speedypotato/Pocket-SDVX/IMAGES/screenshots/100OhmResistor.png

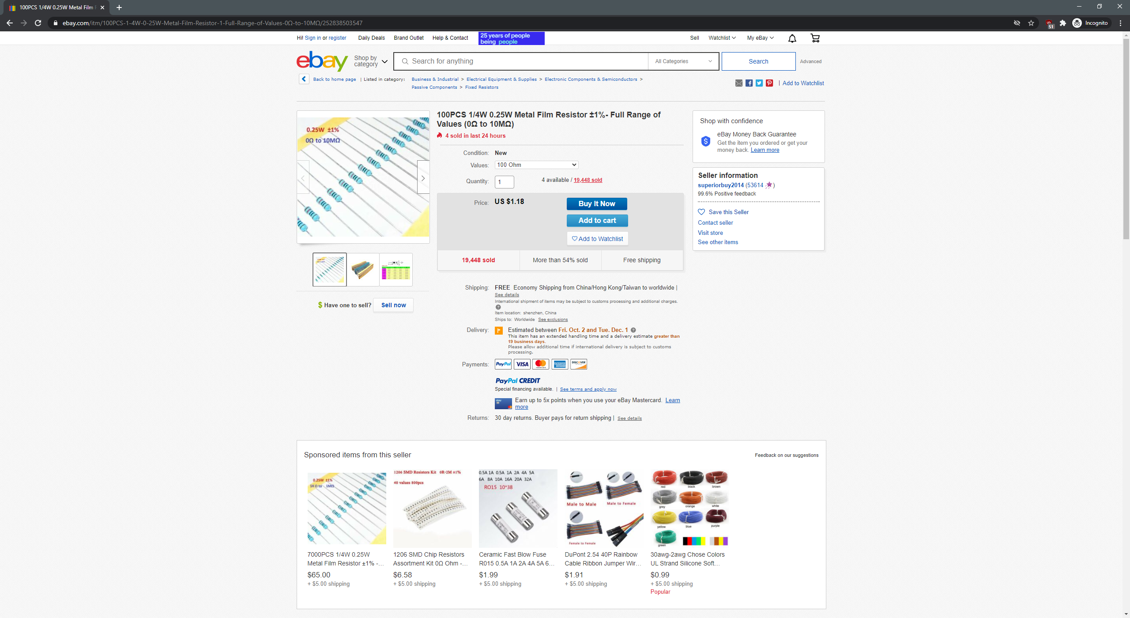
IMAGES/screenshots/100OhmResistor.png
