speedypotato/Pocket-SDVX/IMAGES/screenshots/keycap1x1.png

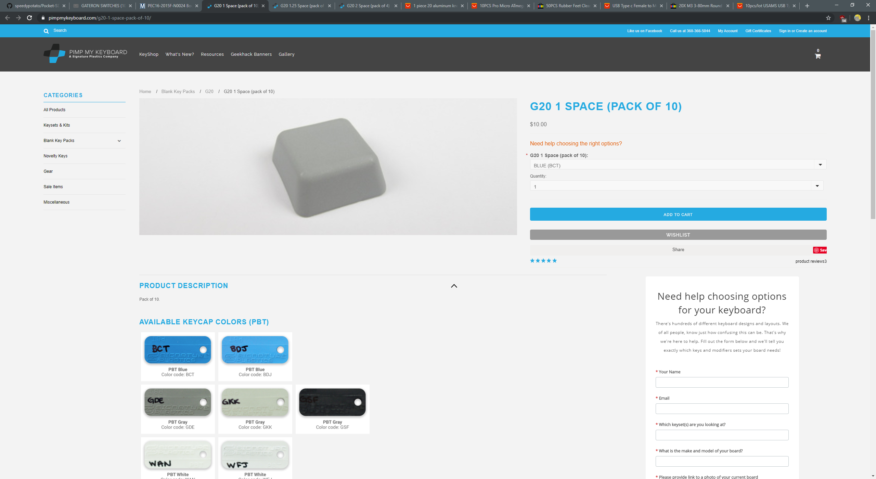
IMAGES/screenshots/keycap1x1.png
