speedypotato/Pocket-SDVX/IMAGES/screenshots/keycap1x2.png

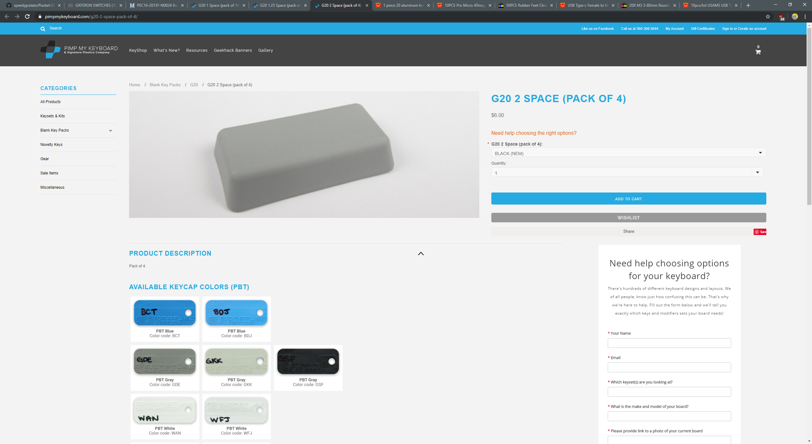
IMAGES/screenshots/keycap1x2.png
