speedypotato/Pocket-SDVX/IMAGES/screenshots/keycap1x125.png

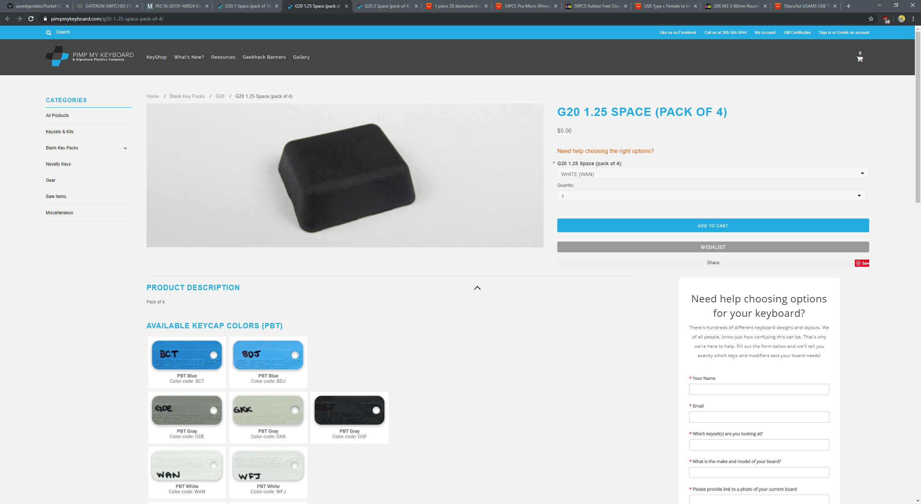
IMAGES/screenshots/keycap1x125.png
