speedypotato/Pocket-SDVX/IMAGES/screenshots/keyswitch.png

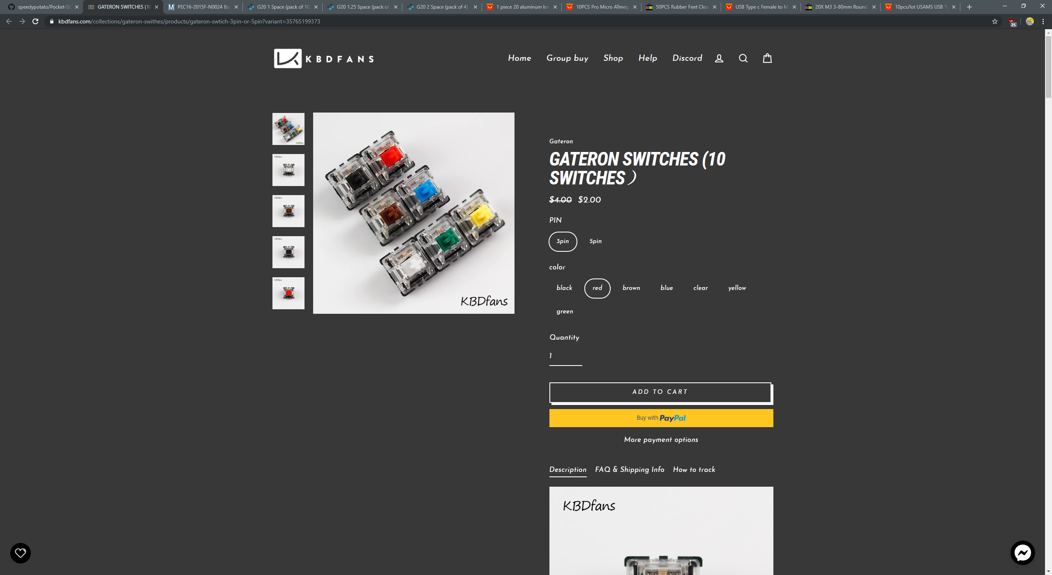
IMAGES/screenshots/keyswitch.png
