speedypotato/Pocket-SDVX/IMAGES/screenshots/knob.png

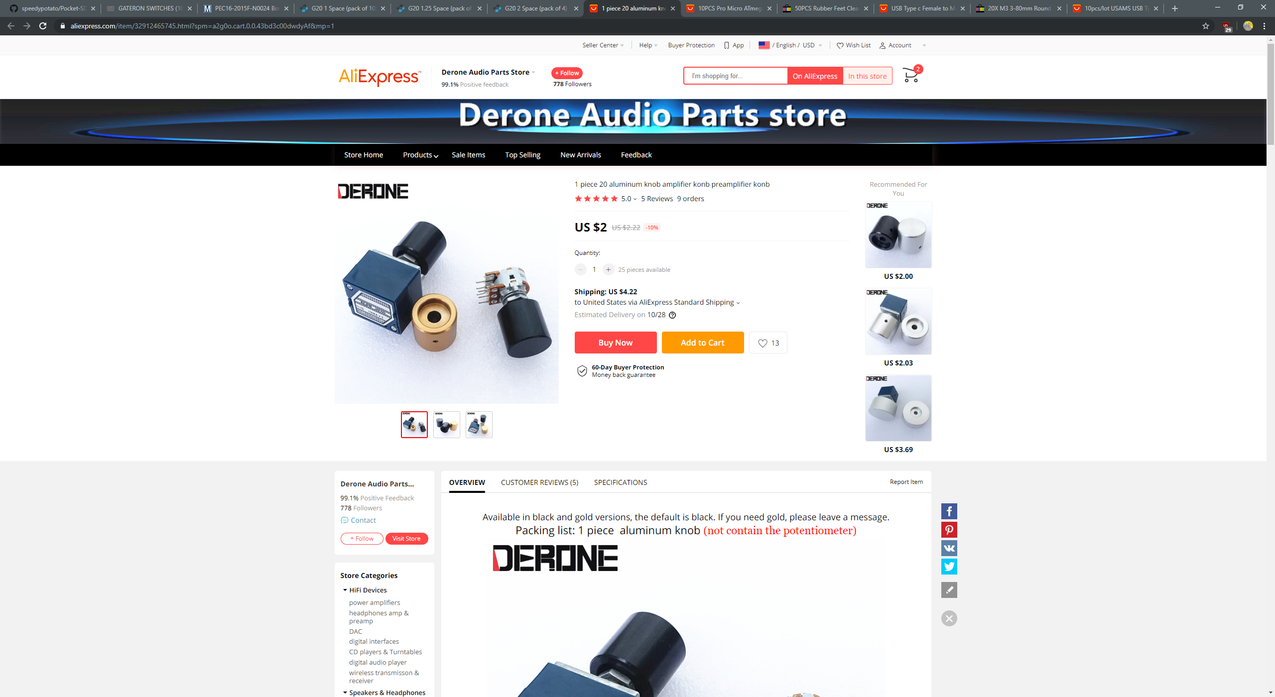
IMAGES/screenshots/knob.png
