speedypotato/Pocket-SDVX/IMAGES/screenshots/promicro.png

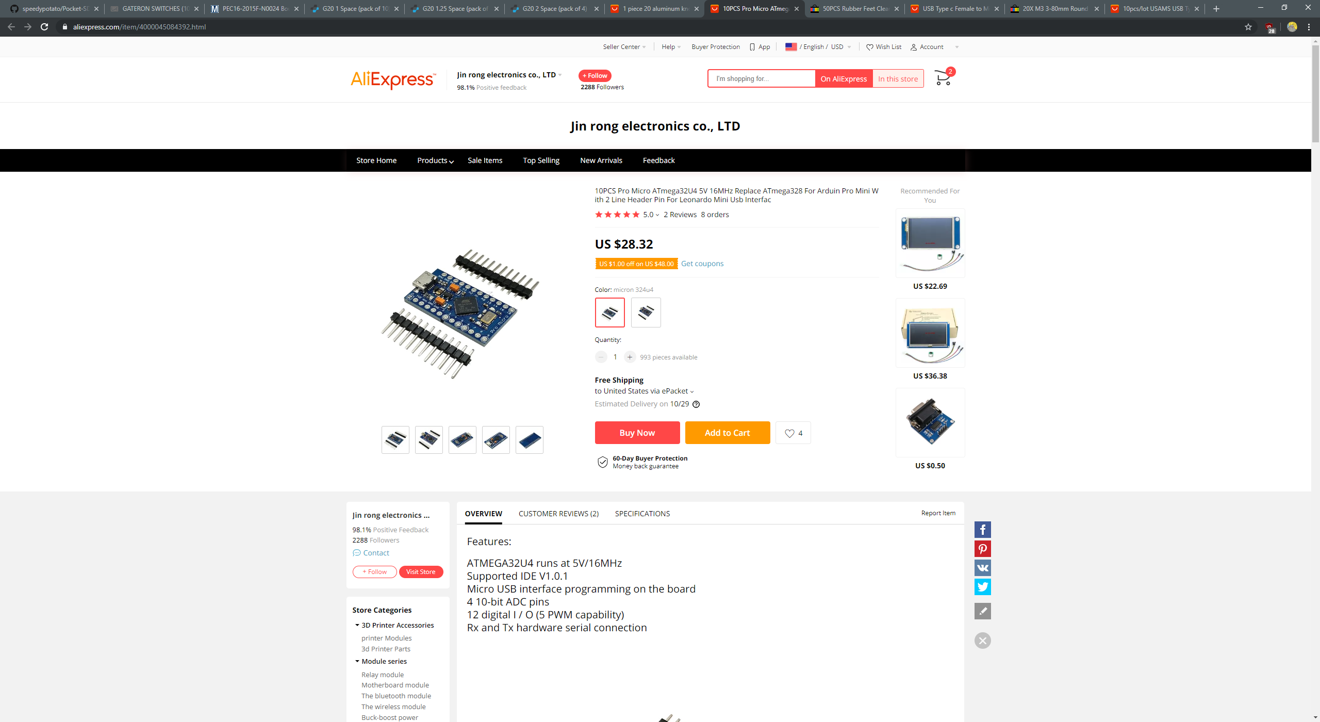
IMAGES/screenshots/promicro.png
