speedypotato/Pocket-SDVX/IMAGES/screenshots/usbcadapter.png

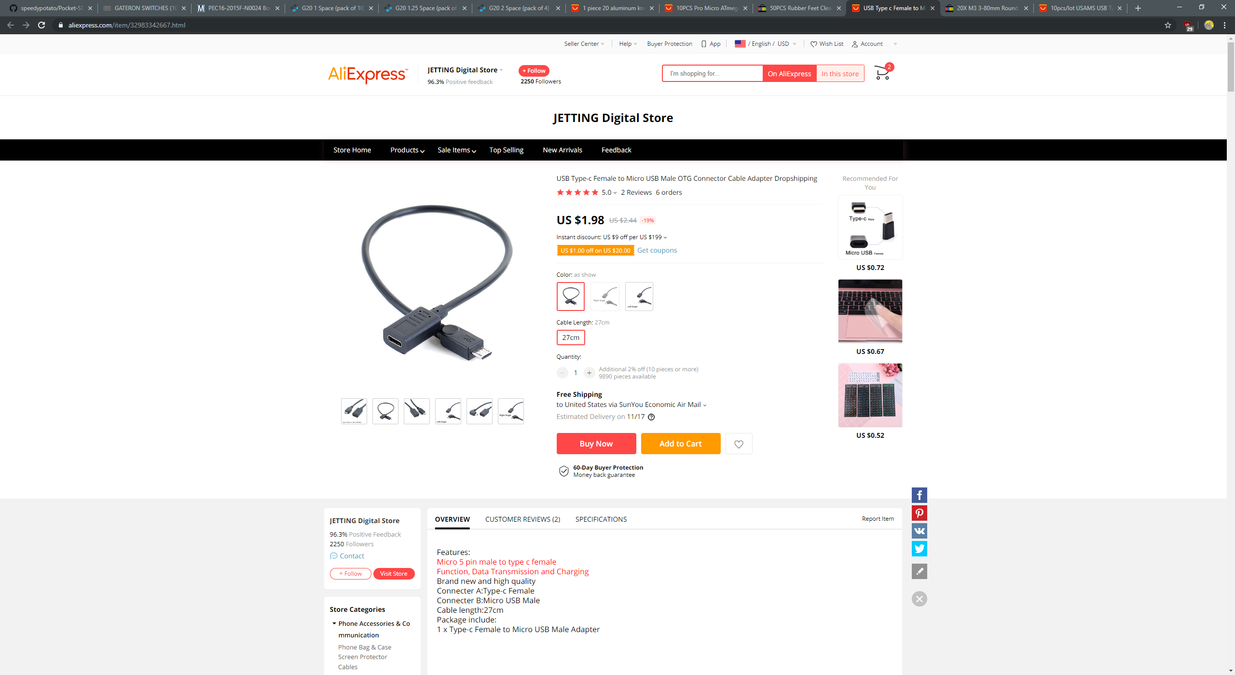
IMAGES/screenshots/usbcadapter.png
