speedypotato/Pocket-SDVX/SKIN/cover_v2.png

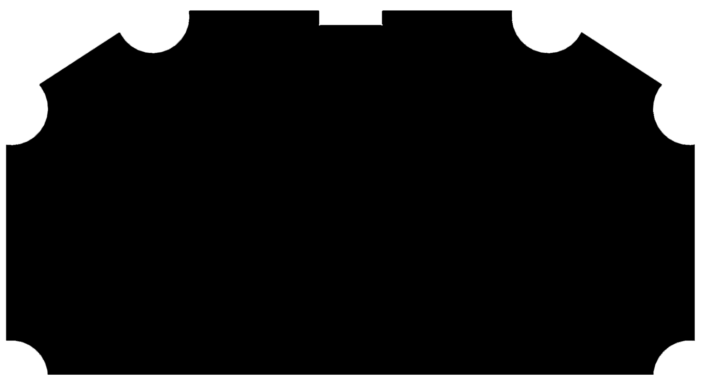
SKIN/cover_v2.png
