speedypotato/Pocket-SDVX/SKIN/layer1.png

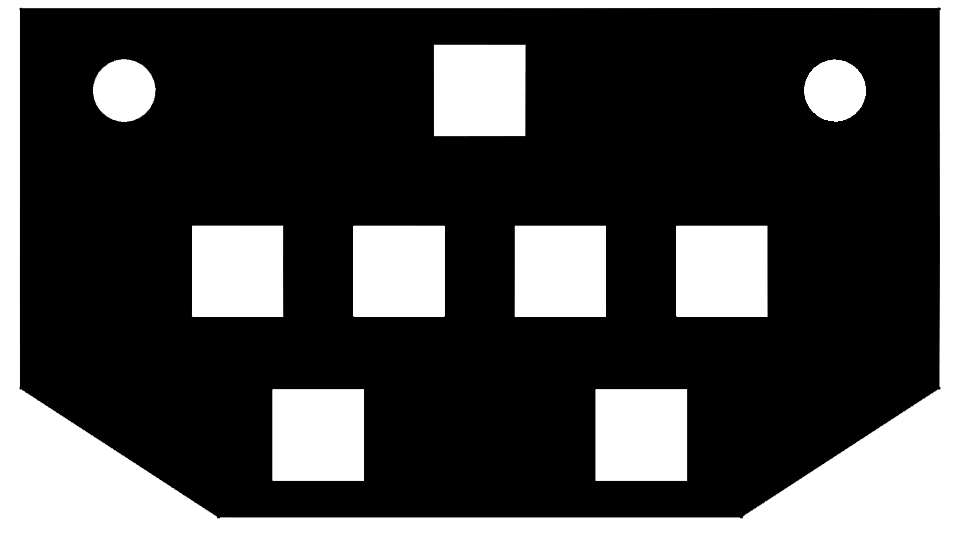
SKIN/layer1.png
