speedypotato/Pocket-SDVX/SKIN/layer2.png

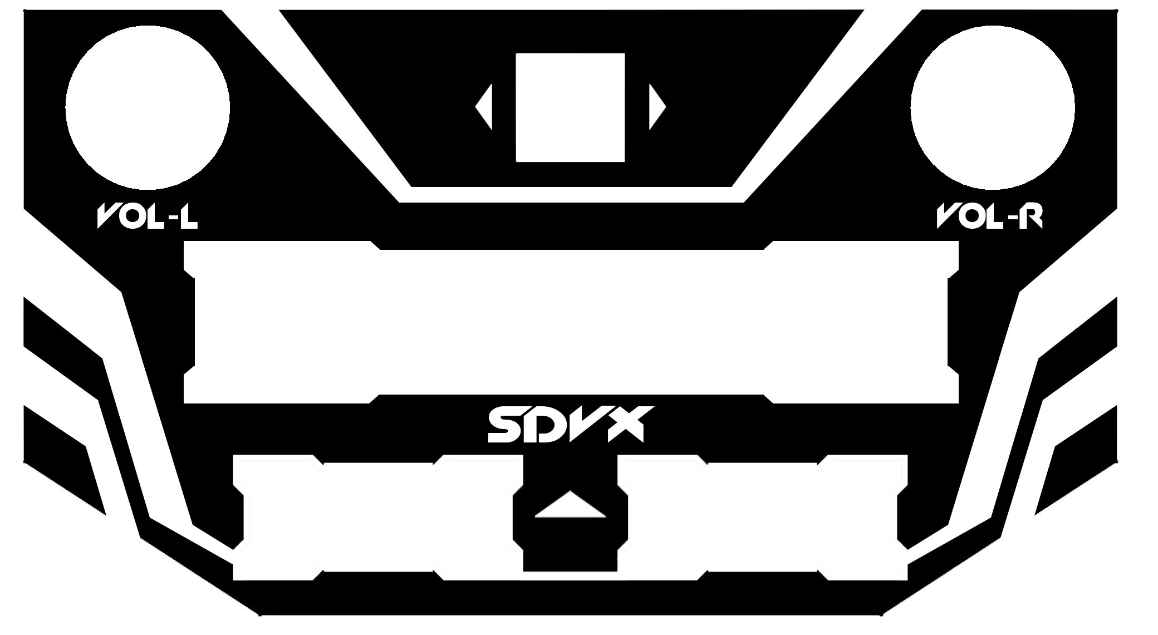
SKIN/layer2.png
